gvi70000/Advanced-Weather-Station-V2/PGA460/PGA460.c

/***************************************************************************
 * @file [PGA460].h/.c
 * This file contains definitions, data structures, and functions
 * for interfacing with the PGA460 ultrasonic transducer driver.
 *
 * Copyright (c) [2024] Grozea Ion gvi70000
 * 
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
 * THE SOFTWARE IS PROVIDED "AS IS", WITHOUT WARRANTY OF ANY KIND, EXPRESS OR
 * IMPLIED, INCLUDING BUT NOT LIMITED TO THE WARRANTIES OF MERCHANTABILITY,
 * FITNESS FOR A PARTICULAR PURPOSE AND NONINFRINGEMENT. IN NO EVENT SHALL THE
 * AUTHORS OR COPYRIGHT HOLDERS BE LIABLE FOR ANY CLAIM, DAMAGES OR OTHER
 * LIABILITY, WHETHER IN AN ACTION OF CONTRACT, TORT OR OTHERWISE, ARISING FROM,
 * OUT OF OR IN CONNECTION WITH THE SOFTWARE OR THE USE OR OTHER DEALINGS IN
 * THE SOFTWARE.
 ***************************************************************************/

// TO BE USED WITH PGA460 Configuration Tool.html to generate registers values

#include <string.h>
#include <stdio.h>
#include <math.h>
#include "usart.h"
#include "tim.h"
#include "PGA460.h"
#include "debug.h"
#include "cordic.h"         /* CORDIC peripheral for atan2 and sqrt */

extern UART_HandleTypeDef huart3;
// Timeout for blocking UART transfers (ms). Increase for low baud rates.
#define PGA460_UART_TIMEOUT_MS  50U
// Array to hold the moment in time when the DECPL pin of each PGA460 goes high filled by TIM2 CH1/2/3 DM
extern volatile DecplTimes_t  ToF_Result[3];  
extern volatile uint8_t Decpl_RDY;


#ifndef M_PI
	#define M_PI 3.14159265358979323846f
#endif

// Conversion factor: half round-trip, microseconds ? seconds
#define TOF_US_TO_S					(1e-6f)   // = 1f * 1e-6
// Geometry 
// 3 transducers on a circle: cone base D = 100 mm, at 120deg.
// They form a cone with the reflector in the tip at 150mm from the base
// The cone semi angle is 17.745deg, the Tx-Reflector-Rx distance is 2x157.493=314.986mm
// if c=496um/us the burst will get to receiver after 635us
// if c=306um/us the burst will get to receiver after 1036us
// 6 pulses at 58kHz are 104us
// Time window of interst is from 600us to 1200us
	
#define PGA460_BASE_DIAMETER_UM				100000	// In micro meters
#define PGA460_DISTANCE_UM						316228	// In micro meters
#define PGA460_CAPTURE_DELAY_MS				70			// Delay for sensor measurement to complete

#define PGA_CMD_SIZE				3
#define PGA_READ_SIZE				4
#define PGA_WRITE_SIZE			5
#define PGA_CMD_COUNT				26
#define PGA_MAX_OBJECTS			8 // PGA460 supports up to 8 objects per measurement
#define PGA_OBJECTS_TRACKED	1	// Number of objects we want to track (Must be = PGA_MAX_OBJECTS)

#if PGA_OBJECTS_TRACKED > PGA_MAX_OBJECTS
	#error "PGA_OBJECTS_TRACKED cannot be greater than PGA_MAX_OBJECTS!"
#endif
#define PGA_OBJ_DATA_SIZE (2 + (PGA_OBJECTS_TRACKED * 4))

#define PGA460_TEMP_ERR	900.0f
#define ULTRASONIC_SENSOR_COUNT	3	// Number of ultrasonic sensors in the array

static const PGA460_Regs_t s0 = {
		.EEData.UserData = {0}, // 0x00..0x13
		.EEData.TVG = {
		.TVGAIN0 = 48, .TVGAIN1 = 80, .TVGAIN2 = 0, .TVGAIN3 = 255,
		.TVGAIN4 = 240, .TVGAIN5 = 0, .TVGAIN6 = 0
	},
	.EEData.Sett = {
		.INIT_GAIN		= 0,		// low initial gain (near target)
		.FREQUENCY		= 144,	// 58.0 kHz (0.2*140+30) CUSA center freq
		.DEADTIME			= 0,		// deglitch=32 us, pulse DT=0
		.PULSE_P1			= 102,	// IO_IF_SEL=0 (time-based), DIAG=1, P1=4 pulses
		.PULSE_P2			= 0,		// P2=0 pulses (addr=0)
		.CURR_LIM_P1	= 63,		// keep your hardware-safe limits
		.CURR_LIM_P2	= 0,
		.REC_LENGTH		= 0,		// 4.096 ms window per preset
		.FREQ_DIAG		= 16,		// standard diag enable
		.SAT_FDIAG_TH	= 0,		// TI typical
		.FVOLT_DEC		= 0,		// TI typical
		.DECPL_TEMP		= 0,		// TI typical
		.DSP_SCALE		= 0,
		.TEMP_TRIM		= 136,
		.P1_GAIN_CTRL = 0,
		.P2_GAIN_CTRL = 0
	},
		.eeCtrl = { .Val.Value = 0 },
//		.Filters = {
//		.BPF_A2_MSB=137, .BPF_A2_LSB=97, .BPF_A3_MSB=252, .BPF_A3_LSB=206, .BPF_B1_MSB=1,
//		.BPF_B1_LSB=153, .LPF_A2_MSB=128, .LPF_A2_LSB=205, .LPF_B1_MSB=0, .LPF_B1_LSB=103
//	},
//		.TestMux = { .Val.Value = 0 },
		.Stat0 = { .Val.Value = 0 },
		.Stat1 = { .Val.Value = 0 },
		.THR = {
		.P1_THR = {49, 65, 0, 0, 0, 0, 255, 255, 255, 255, 255, 255, 255, 255, 255, 7},
		.P2_THR = {49, 65, 0, 0, 0, 0, 248, 1, 255, 255, 255, 255, 255, 255, 255, 7}
		}
	};

static const PGA460_Regs_t s1 = {
		.EEData.UserData = {0}, // 0x00..0x13
		.EEData.TVG = {
		.TVGAIN0 = 48, .TVGAIN1 = 80, .TVGAIN2 = 0, .TVGAIN3 = 255,
		.TVGAIN4 = 240, .TVGAIN5 = 0, .TVGAIN6 = 0
	},
	.EEData.Sett = {
		.INIT_GAIN		= 0,		// low initial gain (near target)
		.FREQUENCY		= 144,	// 58.0 kHz (0.2*140+30) CUSA center freq
		.DEADTIME			= 0,		// deglitch=32 us, pulse DT=0
		.PULSE_P1			= 102,	// IO_IF_SEL=0 (time-based), DIAG=1, P1=4 pulses
		.PULSE_P2			= 32,		// P2=0 pulses (addr=0)
		.CURR_LIM_P1	= 63,		// keep your hardware-safe limits
		.CURR_LIM_P2	= 0,
		.REC_LENGTH		= 0,		// 4.096 ms window per preset
		.FREQ_DIAG		= 16,		// standard diag enable
		.SAT_FDIAG_TH	= 0,		// TI typical
		.FVOLT_DEC		= 0,		// TI typical
		.DECPL_TEMP		= 0,		// TI typical
		.DSP_SCALE		= 0,
		.TEMP_TRIM		= 136,
		.P1_GAIN_CTRL = 0,
		.P2_GAIN_CTRL = 0
	},
		.eeCtrl = { .Val.Value = 0 },
//		.Filters = {
//		.BPF_A2_MSB=137, .BPF_A2_LSB=97, .BPF_A3_MSB=252, .BPF_A3_LSB=206, .BPF_B1_MSB=1,
//		.BPF_B1_LSB=153, .LPF_A2_MSB=128, .LPF_A2_LSB=205, .LPF_B1_MSB=0, .LPF_B1_LSB=103
//	},
//		.TestMux = { .Val.Value = 0 },
		.Stat0 = { .Val.Value = 0 },
		.Stat1 = { .Val.Value = 0 },
		.THR = {
		.P1_THR = {49, 65, 0, 0, 0, 0, 255, 255, 255, 255, 255, 255, 255, 255, 255, 7},
		.P2_THR = {49, 65, 0, 0, 0, 0, 248, 1, 255, 255, 255, 255, 255, 255, 255, 7}
		}
	};

static const PGA460_Regs_t s2 = {
		.EEData.UserData = {0}, // 0x00..0x13
		.EEData.TVG = {
		.TVGAIN0 = 48, .TVGAIN1 = 80, .TVGAIN2 = 0, .TVGAIN3 = 255,
		.TVGAIN4 = 240, .TVGAIN5 = 0, .TVGAIN6 = 0
	},
	.EEData.Sett = {
		.INIT_GAIN		= 0,		// low initial gain (near target)
		.FREQUENCY		= 144,	// 58.0 kHz (0.2*140+30) CUSA center freq
		.DEADTIME			= 0,		// deglitch=32 us, pulse DT=0
		.PULSE_P1			= 102,	// IO_IF_SEL=0 (time-based), DIAG=1, P1=4 pulses
		.PULSE_P2			= 64,		// P2=0 pulses (addr=0)
		.CURR_LIM_P1	= 63,		// keep your hardware-safe limits
		.CURR_LIM_P2	= 0,
		.REC_LENGTH		= 0,		// 4.096 ms window per preset
		.FREQ_DIAG		= 16,		// standard diag enable
		.SAT_FDIAG_TH	= 0,		// TI typical
		.FVOLT_DEC		= 0,		// TI typical
		.DECPL_TEMP		= 0,		// TI typical
		.DSP_SCALE		= 0,
		.TEMP_TRIM		= 136,
		.P1_GAIN_CTRL = 0,
		.P2_GAIN_CTRL = 0
	},
		.eeCtrl = { .Val.Value = 0 },
//		.Filters = {
//		.BPF_A2_MSB=137, .BPF_A2_LSB=97, .BPF_A3_MSB=252, .BPF_A3_LSB=206, .BPF_B1_MSB=1,
//		.BPF_B1_LSB=153, .LPF_A2_MSB=128, .LPF_A2_LSB=205, .LPF_B1_MSB=0, .LPF_B1_LSB=103
//	},
//		.TestMux = { .Val.Value = 0 },
		.Stat0 = { .Val.Value = 0 },
		.Stat1 = { .Val.Value = 0 },
		.THR = {
		.P1_THR = {49, 65, 0, 0, 0, 0, 255, 255, 255, 255, 255, 255, 255, 255, 255, 7},
		.P2_THR = {49, 65, 0, 0, 0, 0, 248, 1, 255, 255, 255, 255, 255, 255, 255, 7}
		}
	};

// --- Array with 3 elements(sensors): [0] TVG, [1] Settings, [2] Thresholds ---
PGA460_Sensor_t sensors[ULTRASONIC_SENSOR_COUNT] = {{ .Registers = s0 }, { .Registers = s1 }, { .Registers = s2 }};

/**
 * @brief Read all EEPROM registers individually and log them via DEBUG().
 * @details Iterates addresses 0x00-0x2B, reads each with PGA460_RegisterRead(),
 *          and logs the named value.  Used during development to verify EEPROM
 *          contents after a bulk write or burn.
 *
 *          ONLY compiled when DEBUG_PGA460 is defined — each register read
 *          incurs a HAL_Delay(100), so the full scan takes ~4.4 s per sensor.
 *          Never call this in production firmware.
 * @param sensorID  Sensor UART address (0-7).
 */
#ifdef DEBUG_PGA460
static void PGA460_ReadAndPrintEEPROM(uint8_t sensorID) {
	DEBUG("Reading EEPROM registers for Sensor %u...\n", sensorID);
	uint8_t regValue = 0;
	for (uint8_t regAddr = 0x00; regAddr <= 0x2B; ++regAddr) {
		if (PGA460_RegisterRead(sensorID, regAddr, &regValue) == HAL_OK) {
			const char* regName;
			switch (regAddr) {
				case REG_USER_DATA1:  regName = "USER_DATA1";  break;
				case REG_USER_DATA2:  regName = "USER_DATA2";  break;
				case REG_USER_DATA3:  regName = "USER_DATA3";  break;
				case REG_USER_DATA4:  regName = "USER_DATA4";  break;
				case REG_USER_DATA5:  regName = "USER_DATA5";  break;
				case REG_USER_DATA6:  regName = "USER_DATA6";  break;
				case REG_USER_DATA7:  regName = "USER_DATA7";  break;
				case REG_USER_DATA8:  regName = "USER_DATA8";  break;
				case REG_USER_DATA9:  regName = "USER_DATA9";  break;
				case REG_USER_DATA10: regName = "USER_DATA10"; break;
				case REG_USER_DATA11: regName = "USER_DATA11"; break;
				case REG_USER_DATA12: regName = "USER_DATA12"; break;
				case REG_USER_DATA13: regName = "USER_DATA13"; break;
				case REG_USER_DATA14: regName = "USER_DATA14"; break;
				case REG_USER_DATA15: regName = "USER_DATA15"; break;
				case REG_USER_DATA16: regName = "USER_DATA16"; break;
				case REG_USER_DATA17: regName = "USER_DATA17"; break;
				case REG_USER_DATA18: regName = "USER_DATA18"; break;
				case REG_USER_DATA19: regName = "USER_DATA19"; break;
				case REG_USER_DATA20: regName = "USER_DATA20"; break;
				case REG_TVGAIN0:     regName = "TVGAIN0";     break;
				case REG_TVGAIN1:     regName = "TVGAIN1";     break;
				case REG_TVGAIN2:     regName = "TVGAIN2";     break;
				case REG_TVGAIN3:     regName = "TVGAIN3";     break;
				case REG_TVGAIN4:     regName = "TVGAIN4";     break;
				case REG_TVGAIN5:     regName = "TVGAIN5";     break;
				case REG_TVGAIN6:     regName = "TVGAIN6";     break;
				case REG_INIT_GAIN:   regName = "INIT_GAIN";   break;
				case REG_FREQUENCY:   regName = "FREQUENCY";   break;
				case REG_DEADTIME:    regName = "DEADTIME";    break;
				case REG_PULSE_P1:    regName = "PULSE_P1";    break;
				case REG_PULSE_P2:    regName = "PULSE_P2";    break;
				case REG_CURR_LIM_P1: regName = "CURR_LIM_P1"; break;
				case REG_CURR_LIM_P2: regName = "CURR_LIM_P2"; break;
				case REG_REC_LENGTH:  regName = "REC_LENGTH";  break;
				case REG_FREQ_DIAG:   regName = "FREQ_DIAG";   break;
				case REG_SAT_FDIAG_TH:regName = "SAT_FDIAG_TH";break;
				case REG_FVOLT_DEC:   regName = "FVOLT_DEC";   break;
				case REG_DECPL_TEMP:  regName = "DECPL_TEMP";  break;
				case REG_DSP_SCALE:   regName = "DSP_SCALE";   break;
				case REG_TEMP_TRIM:   regName = "TEMP_TRIM";   break;
				case REG_P1_GAIN_CTRL:regName = "P1_GAIN_CTRL";break;
				case REG_P2_GAIN_CTRL:regName = "P2_GAIN_CTRL";break;
				case REG_EE_CRC:      regName = "EE_CRC";      break;
				default:              regName = "UNKNOWN";      break;
			}
			DEBUG("  %s = 0x%02X\n", regName, regValue);
		} else {
			DEBUG("  0x%02X: read FAILED\n", regAddr);
		}
		HAL_Delay(100);
	}
	DEBUG("EEPROM read complete for sensor %u.\n", sensorID);
}
#endif /* DEBUG_PGA460 */

/**
 * @brief Compute the PGA460 UART frame checksum.
 * @details Sums all bytes in data[], folds any carry exceeding 0xFF by subtracting 255,
 *          and returns the bitwise complement of the 8-bit result.  The PGA460 protocol
 *          requires this checksum as the final byte of every outgoing frame.
 * @param data  Pointer to the byte array to checksum (typically CMD + payload).
 * @param len  Number of bytes to include in the sum.
 * @return Ones-complement checksum byte.
 */
static uint8_t PGA460_CalculateChecksum(const uint8_t *data, uint8_t len) {
	uint16_t carry = 0;
	for (uint8_t i = 0; i < len; i++) {
		carry += data[i];
		if (carry > 0xFF) {
			carry -= 255;
		}
	}
	return (uint8_t)(~carry & 0xFF);
}

/**
 * @brief Unlock or lock the PGA460 EEPROM by writing REG_EE_CTRL (0x40).
 * @details Sends a single-register write with PGA460_UNLOCK_EEPROM (0x68) to enable
 *          programming, or PGA460_LOCK_EEPROM (0x69) to trigger the burn and lock.
 *          Updates sensors[sensorID].Registers.eepromUnlocked on success.
 * @param sensorID  Sensor UART address (0-7).
 * @param unlock  1 = unlock (write 0x68); 0 = lock/burn (write 0x69).
 * @return HAL status.
 */
static HAL_StatusTypeDef PGA460_SetEEPROMAccess(const uint8_t sensorID, const uint8_t unlock) {
	uint8_t accessByte = unlock ? PGA460_UNLOCK_EEPROM : PGA460_LOCK_EEPROM;
	uint8_t cmd[5] = {PGA460_SYNC, (uint8_t)((sensorID << 5) | PGA460_CMD_REGISTER_WRITE), REG_EE_CTRL, accessByte, 0};
	cmd[4] = PGA460_CalculateChecksum(&cmd[1], 3); // Checksum over CMD, ADDR, DATA
	if (HAL_UART_Transmit(&huart3, cmd, sizeof(cmd), PGA460_UART_TIMEOUT_MS) != HAL_OK) {
		DEBUG("Sensor %d: EEPROM %s failed\n", sensorID, unlock ? "unlock" : "lock");
		return HAL_ERROR;
	}
	// Update status flag on success
	sensors[sensorID].Registers.eepromUnlocked = unlock ? 1 : 0;
	return HAL_OK;
}

/**
 * @brief PGA460_ScanAndReport function implementation.
 * @details Probes UART addresses 0-7 by reading REG_PULSE_P2 from each.  For each
 *          responding sensor, prints the UART address, the internal address stored in
 *          PULSE_P2[7:5], and the P2 pulse count.  Flags any address mismatch.
 *          Useful for initial bus setup and after PGA460_WriteUARTAddr().
 */
void PGA460_ScanAndReport(void) {
    uint8_t regValue = 0;
    uint8_t foundCount = 0;
    DEBUG("\n--- PGA460 Bus Scan (Addresses 0-7) ---\n");
    for (uint8_t addr = 0; addr <= 7; addr++) {
        if (PGA460_RegisterRead(addr, REG_PULSE_P2, &regValue) == HAL_OK) {
            foundCount++;
            uint8_t internalAddr = (regValue >> 5);
            uint8_t pulseCount   = (regValue & 0x1F);
            DEBUG("  [+] Sensor at UART addr %u  (stored addr=%u, P2 pulses=%u)\n",
                  addr, internalAddr, pulseCount);
            if (addr != internalAddr) {
                DEBUG("      [!] Address mismatch: listening on %u, register says %u\n",
                      addr, internalAddr);
            }
        }
        HAL_Delay(10);
    }
    if (foundCount == 0) {
        DEBUG("  [-] No sensors detected. Check power and wiring.\n");
    } else {
        DEBUG("--- Scan complete: %u sensor(s) found ---\n\n", foundCount);
    }
}

/**
 * @brief PGA460_WriteUARTAddr function implementation.
 * @details Scans the bus for the first responding sensor, writes the new UART address
 *          to REG_PULSE_P2[7:5] in RAM, then burns it to EEPROM so it persists.
 *          Steps: scan -> wake -> RAM write -> unlock -> burn -> verify.
 * @param targetAddr  New UART address to assign (0-7).
 * @return HAL status.
 */
HAL_StatusTypeDef PGA460_WriteUARTAddr(uint8_t targetAddr) {
uint8_t foundAddr = 0xFF;
    uint8_t regP2 = 0;
    uint8_t eeStatus = 0;
    // 1. SCAN: Find which address (0-7) responds
    for (uint8_t a = 0; a <= 7; a++) {
        if (PGA460_RegisterRead(a, REG_PULSE_P2, &regP2) == HAL_OK) {
            foundAddr = a;
            DEBUG("Found sensor at %u (Register says %u)\n", a, regP2);
            break;
        }
    }
    if (foundAddr == 0xFF) {
        DEBUG("No sensor found on bus.\n");
        return HAL_ERROR;
    }
    // 2. WAKE UP: Move digital core to READY state
    // Mandatory before EEPROM operations.
    PGA460_SetThresholds(foundAddr);
    HAL_Delay(50);
    // 3. RAM UPDATE: Set new address and ensure P2_PULSE = 0
    // Based on your requirement: targetAddr << 5
    uint8_t writeVal = (targetAddr << 5); 
    PGA460_RegisterWrite(foundAddr, REG_PULSE_P2, writeVal);
    HAL_Delay(50);
    // 4. BURN: Commit new address to EEPROM permanently.
    // PGA460_BurnEEPROM performs the full TI-specified two-step sequence
    // (write 0x68, wait 1 ms, write 0x69, wait 1000 ms, verify EE_PRGM_OK).
    // Do NOT write 0x68/0x69 manually here first — that would trigger two
    // consecutive burn cycles, wasting one of the 1000 guaranteed EEPROM cycles.
    DEBUG("Burning Address %u to EEPROM...\n", targetAddr);
    if (PGA460_BurnEEPROM(targetAddr) != HAL_OK) {
        DEBUG("Burn Command failed to send.\n");
        return HAL_ERROR;
    }
    // 5. WAIT & VERIFY
    HAL_Delay(100); // Wait for physical EEPROM write
    PGA460_RegisterRead(targetAddr, 0x40, &eeStatus);
    if (eeStatus & 0x80) {
        DEBUG("EEPROM ERROR: 0x%02X. Burn rejected.\n", eeStatus);
        return HAL_ERROR;
    }
    DEBUG("SUCCESS: Sensor set to Address %u\n", targetAddr);
    return HAL_OK;
}

EEImage_t *PGA460_GetEEData(uint8_t sensorID) {
    if (sensorID >= ULTRASONIC_SENSOR_COUNT) return NULL;
    return &sensors[sensorID].Registers.EEData;
}

/**
 * @brief PGA460_Init function implementation.
 * @details Initialises all three sensors in sequence.  For each sensor:
 *            1. Resets the Measures struct (tof_us, width, amplitude = 0).
 *            2. Writes the threshold map (mandatory to transition out of sleep).
 *          The burnEEPROM path is compiled but commented out; enable it when
 *          the final configuration needs committing to non-volatile storage.
 * @param burnEEPROM  1 = burn configuration to EEPROM flash after writing; 0 = RAM only.
 * @return HAL status.
 */
HAL_StatusTypeDef PGA460_Init(uint8_t burnEEPROM) {
	for (uint8_t i = 0; i < ULTRASONIC_SENSOR_COUNT; ++i) {
		// Step 1: Assign transducer config and reset measures
		sensors[i].Measures.tof_us		= 0;
		sensors[i].Measures.width			= 0;
		sensors[i].Measures.amplitude	= 0;
		// Step 2: Threshold write (uses current sensors[i].Registers.THR) !!! Mandatory step to start the sensor
		if (PGA460_SetThresholds(i) != HAL_OK) {
			DEBUG("Sensor %u: Threshold write failed!\n", i);
			return HAL_ERROR;
		}
		// Step 3: Read back full EEPROM image into sensors[i].Registers.EEData
		// This populates UserData[0..3] so Wind_LoadCalibration() can read path lengths
        if (PGA460_EEPROMBulkRead(i) != HAL_OK) {
            DEBUG("Sensor %u: EEPROM bulk read failed, UserData will be zero\n", i);
            // Non-fatal: Wind_LoadCalibration will fall back to NOMINAL_PATH_UM
        }
#ifdef DEBUG_PGA460
		/* Full register dump — ~4.4 s per sensor; only for bench verification. */
		PGA460_ReadAndPrintEEPROM(i);
#endif /* DEBUG_PGA460 */
//		// Step 2: EEPROM bulk write (shadow -> device)
//		if (PGA460_EEPROMBulkWrite(i) != HAL_OK) {
//			DEBUG("Sensor %u: EEPROM bulk write failed!\n", i);
//			return HAL_ERROR;
//		}
////		PGA460_ReadAndPrintEEPROM(i);
//		if(burnEEPROM) {
//			// Step 3: Optional EEPROM Burn
//			if (PGA460_BurnEEPROM(i) != HAL_OK) {
//				DEBUG("Sensor %u: EEPROM burn failed!\n", i);
//				return HAL_ERROR;
//			}
//		}
//		// Step 4: TVG write (push current TVG from mirror)
//		if (PGA460_SetTVG(i, PGA460_GAIN_58_90dB, &sensors[i].Registers.EEData.TVG) != HAL_OK) {
//				DEBUG("Sensor %u: TVG bulk write failed!\n", i);
//				return HAL_ERROR;
//		}
		// Step 5: Diagnostics/status
//		if (PGA460_CheckStatus(i) != HAL_OK) {
//			DEBUG("Sensor %u: Status check failed!\n", i);
//			//return HAL_ERROR;
//		}
//		// Frequency (Hz) via system diagnostics (diag=0)
//		float diagVal = 0.0f;
//		if (PGA460_GetSystemDiagnostics(i, 1, 0, &diagVal) == HAL_OK)
//				DEBUG("Sensor %u: Frequency Diagnostic = %.2f Hz\n", i, diagVal);
//		if (PGA460_GetSystemDiagnostics(i, 0, 1, &diagVal) == HAL_OK)
//				DEBUG("Sensor %u: Decay Period Diagnostic = %.2f us\n", i, diagVal);
//		if (PGA460_GetSystemDiagnostics(i, 0, 2, &diagVal) == HAL_OK)
//				DEBUG("Sensor %u: Die Temperature = %.2f C\n", i, diagVal);
//		if (PGA460_GetSystemDiagnostics(i, 0, 3, &diagVal) == HAL_OK)
//				DEBUG("Sensor %u: Noise Level = %.0f\n", i, diagVal);
//		// Step 7: Optional Echo Data Dump for verification
//		uint8_t echoBuf[128];
//		if (PGA460_GetEchoDataDump(i, PGA460_CMD_BURST_AND_LISTEN_PRESET1, echoBuf) != HAL_OK) {
//			DEBUG("Sensor %u: Echo Data Dump failed!\n", i);
//			return HAL_ERROR;
//		}
		
//		DEBUG("Sensor %u: Echo Data Dump:\n", i);
//		for (uint8_t j = 0; j < 128; ++j) {
//			DEBUG("%u%s", echoBuf[j], (j < 127) ? "," : "\n");
//		}
		DEBUG("-----\n");
		HAL_Delay(100);
	}
	return HAL_OK;
}

/**
 * @brief PGA460_RegisterRead function implementation.
 * @details Sends a 4-byte TX frame [SYNC][CMD][REG_ADDR][CHK] and reads the
 *          3-byte response [DIAG][DATA][CHK].  The DATA byte is returned in *regValue.
 *          The CMD byte encodes the sensor UART address in bits [7:5].
 * @param sensorID  Sensor UART address (0-7).
 * @param regAddr  Register address to read.
 * @param regValue  Output: register value.
 * @return HAL status.
 */
HAL_StatusTypeDef PGA460_RegisterRead(uint8_t sensorID, uint8_t regAddr, uint8_t *regValue) {
	// --- TX frame: [SYNC][CMD][REG_ADDR][CHK] ---
	uint8_t cmd[4] = {PGA460_SYNC, (uint8_t)((sensorID << 5) | PGA460_CMD_REGISTER_READ), regAddr, 0};
	cmd[3] = PGA460_CalculateChecksum(&cmd[1], 2); // Checksum over CMD + REG_ADDR
	if (HAL_UART_Transmit(&huart3, cmd, sizeof(cmd), PGA460_UART_TIMEOUT_MS) != HAL_OK) return HAL_ERROR;
	// --- RX frame: [DIAG][DATA][CHK] ---
	if (HAL_UART_Receive(&huart3, cmd, 3, PGA460_UART_TIMEOUT_MS) != HAL_OK) return HAL_ERROR;
	*regValue = cmd[1]; // DATA byte
	return HAL_OK;
}

/**
 * @brief PGA460_RegisterWrite function implementation.
 * @details Sends a 5-byte TX frame [SYNC][CMD][REG_ADDR][DATA][CHK].
 *          A 1 ms delay is applied after transmission; increase to 10 ms when writing
 *          TVG, threshold, or gain registers followed immediately by a read.
 * @param sensorID  Sensor UART address (0-7).
 * @param regAddr  Register address to write.
 * @param regValue  Value to write.
 * @return HAL status.
 */
HAL_StatusTypeDef PGA460_RegisterWrite(uint8_t sensorID, uint8_t regAddr, uint8_t regValue) {
	// TX frame: [SYNC][CMD][REG_ADDR][REG_VALUE][CHK]
	uint8_t cmd[5] = {PGA460_SYNC, (uint8_t)((sensorID << 5) | PGA460_CMD_REGISTER_WRITE), regAddr, regValue, 0};
	cmd[4] = PGA460_CalculateChecksum(&cmd[1], 3); // checksum over CMD+ADDR+DATA
	if (HAL_UART_Transmit(&huart3, cmd, sizeof(cmd), PGA460_UART_TIMEOUT_MS) != HAL_OK) return HAL_ERROR;
	// For commands 10 and 22: Wait 60 us if INIT_GAIN, TVG, THR or P1_GAIN_CTRL or P2_GAIN_CTRL
	// is written to before a read, otherwise wait 3.3 us for other functions.
	HAL_Delay(1); // Increase to 10 if needed
	return HAL_OK;
}

/**
 * @brief PGA460_CheckStatus function implementation.
 * @details Reads DEV_STAT0 (0x4C) and DEV_STAT1 (0x4D) and uses DEBUG() to report
 *          any active fault bits: EEPROM CRC errors, wakeup errors, thermal shutdown,
 *          and over/under-voltage conditions on VPWR, AVDD, and IOREG.
 * @param sensorID  Sensor UART address (0-7).
 * @return HAL status.
 */
HAL_StatusTypeDef PGA460_CheckStatus(uint8_t sensorID) {
	// Read both DEV_STAT registers
	if (PGA460_RegisterRead(sensorID, REG_DEV_STAT0, &sensors[sensorID].Registers.Stat0.Val.Value) != HAL_OK || PGA460_RegisterRead(sensorID, REG_DEV_STAT1, &sensors[sensorID].Registers.Stat1.Val.Value) != HAL_OK) {
		DEBUG("Sensor %d: Communication error! Could not read status registers.\n", (int)sensorID);
		return HAL_ERROR;
	}
	// --- DEV_STAT0 Flags ---
	if (sensors[sensorID].Registers.Stat0.Val.BitField.CMW_WU_ERR)
		DEBUG("Sensor %d: [CMW_WU_ERR] Wake-up error!\n", (int)sensorID);
	if (sensors[sensorID].Registers.Stat0.Val.BitField.THR_CRC_ERR)
		DEBUG("Sensor %d: [THR_CRC_ERR] Threshold CRC error!\n", (int)sensorID);
	if (sensors[sensorID].Registers.Stat0.Val.BitField.EE_CRC_ERR)
		DEBUG("Sensor %d: [EE_CRC_ERR] EEPROM CRC error!\n", (int)sensorID);
	if (sensors[sensorID].Registers.Stat0.Val.BitField.TRIM_CRC_ERR)
		DEBUG("Sensor %d: [TRIM_CRC_ERR] Trim CRC error!\n", (int)sensorID);
	// --- DEV_STAT1 Flags ---
	if (sensors[sensorID].Registers.Stat1.Val.BitField.TSD_PROT)
		DEBUG("Sensor %d: [TSD_PROT] Thermal shutdown occurred!\n", (int)sensorID);
	if (sensors[sensorID].Registers.Stat1.Val.BitField.IOREG_OV)
		DEBUG("Sensor %d: [IOREG_OV] IOREG Overvoltage!\n", (int)sensorID);
	if (sensors[sensorID].Registers.Stat1.Val.BitField.IOREG_UV)
		DEBUG("Sensor %d: [IOREG_UV] IOREG Undervoltage!\n", (int)sensorID);
	if (sensors[sensorID].Registers.Stat1.Val.BitField.AVDD_OV)
		DEBUG("Sensor %d: [AVDD_OV] AVDD Overvoltage!\n", (int)sensorID);
	if (sensors[sensorID].Registers.Stat1.Val.BitField.AVDD_UV)
		DEBUG("Sensor %d: [AVDD_UV] AVDD Undervoltage!\n", (int)sensorID);
	if (sensors[sensorID].Registers.Stat1.Val.BitField.VPWR_OV)
		DEBUG("Sensor %d: [VPWR_OV] VPWR Overvoltage!\n", (int)sensorID);
	if (sensors[sensorID].Registers.Stat1.Val.BitField.VPWR_UV)
		DEBUG("Sensor %d: [VPWR_UV] VPWR Undervoltage!\n", (int)sensorID);
	return HAL_OK;
}

/**
 * @brief PGA460_EEPROMBulkWrite function implementation.
 * @details Sends the 43-byte EEPROM payload (UserData[20] + TVG[7] + Settings[16])
 *          using CMD 0x0C.  EE_CRC (register 0x2B, the last byte of Settings_t) is
 *          intentionally excluded — the device auto-calculates and stores it on burn.
 *          Confirmed against TI USSC library calcChecksum (EEBW case): checksumLoops=44
 *          covers CMD + 43 data bytes; EE_CRC is never part of the bulk-write payload.
 *
 *          Frame layout: [SYNC][CMD][43 bytes][CHK]  = 45 bytes total.
 *          Checksum input: CMD + 43 data bytes = 44 bytes.
 * @param sensorID  Sensor UART address (0-7).
 * @return HAL status.
 */
HAL_StatusTypeDef PGA460_EEPROMBulkWrite(uint8_t sensorID) {
	// Step 1: Unlock EEPROM if needed
	if (sensors[sensorID].Registers.eepromUnlocked == 0) {
		if (PGA460_SetEEPROMAccess(sensorID, 1) != HAL_OK) {
			DEBUG("Sensor %d: EEPROM unlock failed before bulk write\n", sensorID);
			return HAL_ERROR;
		}
	}
	/* Step 2: Build 45-byte frame.
	 * EEImage_t = UserData[20] + TVG[7] + Settings[17] = 44 bytes.
	 * The last Settings byte is EE_CRC (auto-computed by the device; must NOT be
	 * sent).  We copy only 43 bytes (sizeof(EEImage_t) - 1).               */
	uint8_t frame[45] = {0};
	frame[0] = PGA460_SYNC;
	frame[1] = (uint8_t)((sensorID << 5) | PGA460_CMD_EEPROM_BULK_WRITE);
	memcpy(&frame[2], &sensors[sensorID].Registers.EEData, sizeof(EEImage_t) - 1u); /* 43 bytes, no EE_CRC */
	/* Checksum: CMD (frame[1]) + 43 data bytes = 44 inputs */
	frame[44] = PGA460_CalculateChecksum(&frame[1], 44u);
	// Step 3: Transmit
	if (HAL_UART_Transmit(&huart3, frame, sizeof(frame), PGA460_UART_TIMEOUT_MS) != HAL_OK) {
		DEBUG("Sensor %d: EEPROM Bulk Write Failed!\n", sensorID);
		return HAL_ERROR;
	}
	HAL_Delay(1);
	if (PGA460_SetEEPROMAccess(sensorID, 0) != HAL_OK) {
		DEBUG("Sensor %d: EEPROM lock failed after bulk write\n", sensorID);
		return HAL_ERROR;
	}
	return HAL_OK;
}

/**
 * @brief PGA460_EEPROMBulkRead function implementation.
 * @details Sends CMD 0x0B (EEPROM Bulk Read) and receives the 46-byte response:
 *          [DIAG][44 EEData bytes][CHK].  The 44 bytes are copied directly into
 *          sensors[sensorID].Registers.EEData, populating UserData[0..19], TVG,
 *          and Settings in one shot.  This must be called during PGA460_Init()
 *          so that Wind_LoadCalibration() can read path lengths from UserData[0..3].
 * @param sensorID  Sensor UART address (0-7).
 * @return HAL status.
 */
HAL_StatusTypeDef PGA460_EEPROMBulkRead(uint8_t sensorID) {
    // TX frame: [SYNC][CMD][CHK] ? 3 bytes
    uint8_t tx[3];
    tx[0] = PGA460_SYNC;
    tx[1] = (uint8_t)((sensorID << 5) | PGA460_CMD_EEPROM_BULK_READ);
    tx[2] = PGA460_CalculateChecksum(&tx[1], 1);

    if (HAL_UART_Transmit(&huart3, tx, sizeof(tx), PGA460_UART_TIMEOUT_MS) != HAL_OK) {
        DEBUG("Sensor %u: EEPROM Bulk Read TX failed\n", sensorID);
        return HAL_ERROR;
    }

    // RX frame: [DIAG][44 EEData bytes][CHK] ? 46 bytes
    uint8_t rx[46] = {0};
    if (HAL_UART_Receive(&huart3, rx, sizeof(rx), PGA460_UART_TIMEOUT_MS) != HAL_OK) {
        DEBUG("Sensor %u: EEPROM Bulk Read RX failed\n", sensorID);
        return HAL_ERROR;
    }

    // rx[0] = DIAG, rx[1..44] = EEData, rx[45] = CHK
    memcpy(&sensors[sensorID].Registers.EEData, &rx[1], sizeof(EEImage_t));

    DEBUG("Sensor %u: EEPROM Bulk Read OK - UserData[0..3] = %02X %02X %02X %02X\n",
          sensorID,
          sensors[sensorID].Registers.EEData.UserData[0],
          sensors[sensorID].Registers.EEData.UserData[1],
          sensors[sensorID].Registers.EEData.UserData[2],
          sensors[sensorID].Registers.EEData.UserData[3]);

    return HAL_OK;
}

/**
 * @brief PGA460_BurnEEPROM function implementation.
 * @details Executes the TI-specified two-step burn sequence on REG_EE_CTRL (0x40):
 *            1. Write 0x68 to begin the unlock sequence.
 *            2. Write 0x69 to start the internal charge pump and program the EEPROM.
 *            3. Wait 1000 ms (TI minimum; do not interrupt the sensor during this time).
 *            4. Read EE_CTRL back and verify bit 2 (EE_PRGM_OK) is set.
 *            5. Write 0x00 to leave EE_CTRL in a clean state.
 *          Use sparingly: the PGA460 EEPROM supports a limited number of burn cycles.
 * @param sensorID  Sensor UART address (0-7).
 * @return HAL status.
 */
HAL_StatusTypeDef PGA460_BurnEEPROM(uint8_t sensorID) {
    uint8_t burnStat = 0;
    // 1. Unlock EEPROM (0x68)
    if (PGA460_RegisterWrite(sensorID, 0x40, 0x68) != HAL_OK) {
        return HAL_ERROR;
    }
    HAL_Delay(1); // Short pause between unlock steps
    // 2. Trigger Burn (0x69)
    // Writing 0x69 sets the EEPRGM bit which initiates the internal charge pump
    if (PGA460_RegisterWrite(sensorID, 0x40, 0x69) != HAL_OK) {
        return HAL_ERROR;
    }
    // 3. WAIT (Crucial!) 
    // TI uses 1000ms. The process is slow. Do not interrupt the sensor here.
    HAL_Delay(1000);
    // 4. Read back status from EE_CNTRL
    if (PGA460_RegisterRead(sensorID, 0x40, &burnStat) != HAL_OK) {
        return HAL_ERROR;
    }
    // 5. Check Bit 2 (EE_PRGM_OK)
    if ((burnStat & 0x04) == 0x04) {
        DEBUG("Sensor %u: EEPROM Burn Successful (Status: 0x%02X)\n", sensorID, burnStat);
        // TI-style cleanup: Set back to 0 to lock
        PGA460_RegisterWrite(sensorID, 0x40, 0x00);
        return HAL_OK;
    } else {
        DEBUG("Sensor %u: Burn Failed (Status: 0x%02X, expected bit 2 set)\n", sensorID, burnStat);
        return HAL_ERROR;
    }
}

/**
 * @brief PGA460_GetTVG function implementation.
 * @details Sends CMD 0x0D (TVG Bulk Read) and receives [DIAG][TVGAIN0..TVGAIN6]
 *          (8 bytes total).  The 7 TVG bytes are copied into
 *          sensors[sensorID].Registers.EEData.TVG.  Returns HAL_ERROR if the
 *          response is all 0xFF (UART idle flood).
 * @param sensorID  Sensor UART address (0-7).
 * @return HAL status.
 */
HAL_StatusTypeDef PGA460_GetTVG(uint8_t sensorID) {
	// Send command [SYNC][CMD][CHK]
	uint8_t tx[3];
	tx[0] = PGA460_SYNC; // 0x55
	tx[1] = (uint8_t)((sensorID << 5) | (PGA460_CMD_TVG_BULK_READ)); // Command code
	tx[2] = PGA460_CalculateChecksum(&tx[1], 1);
	if (HAL_UART_Transmit(&huart3, tx, sizeof(tx), PGA460_UART_TIMEOUT_MS) != HAL_OK) {
		return HAL_ERROR;
	}
	// --- Step 2: Receive DIAG + 7 TVG bytes ---
	// RX: [DIAG][TVGAIN0..TVGAIN6] => 1 + 7 = 8 bytes
	uint8_t rx[8] = {0};
	if (HAL_UART_Receive(&huart3, rx, sizeof(rx), PGA460_UART_TIMEOUT_MS) != HAL_OK) {
		return HAL_ERROR;
	}
	// Optional: detect idle flood (all 0xFF)
	uint8_t idle = 1;
	for (uint32_t i = 0; i < sizeof(rx); i++) {
		if (rx[i] != 0xFF) {
			idle = 0;
			break;
		}
	}
	if (idle) return HAL_ERROR;
	// --- Step 3: Copy TVG bytes into mirror (skip rx[0] = DIAG) ---
	memcpy(&sensors[sensorID].Registers.EEData.TVG, &rx[1], sizeof(TVG_t));
	return HAL_OK;
}

/**
 * @brief PGA460_SetTVG function implementation.
 * @details Updates DECPL_TEMP[7:6] with the requested AFE gain range (preserving the
 *          lower 6 bits), then sends CMD 0x0E (TVG Bulk Write) with the 7-byte TVG
 *          payload.  Mirrors the written values into sensors[sensorID].Registers.
 * @param sensorID  Sensor UART address (0-7).
 * @param gain_range  AFE gain range (see PGA460_GainRange_t).
 * @param tvg  Pointer to the 7-byte TVG profile to write.
 * @return HAL status.
 */
HAL_StatusTypeDef PGA460_SetTVG(uint8_t sensorID, PGA460_GainRange_t gain_range, const TVG_t *tvg) {
	// 1) Update DECPL_TEMP[7:6] = AFE_GAIN_RNG, preserve other bits.
	sensors[sensorID].Registers.EEData.Sett.DECPL_TEMP = (sensors[sensorID].Registers.EEData.Sett.DECPL_TEMP & 0x3F) | gain_range;
	if (PGA460_RegisterWrite(sensorID, REG_DECPL_TEMP, sensors[sensorID].Registers.EEData.Sett.DECPL_TEMP) != HAL_OK) {
		return HAL_ERROR;
	}
	// 2) TVG bulk write: [SYNC][CMD=0x0E][7 TVG bytes][CHK]
	uint8_t frame[10];
	frame[0] = PGA460_SYNC;
	frame[1] = (uint8_t)((sensorID << 5) | (PGA460_CMD_TVG_BULK_WRITE));
	memcpy(&frame[2], tvg, sizeof(TVG_t)); // 7 bytes payload
	frame[9] = PGA460_CalculateChecksum(&frame[1], 1 + sizeof(TVG_t)); // checksum over CMD+DATA
	if (HAL_UART_Transmit(&huart3, frame, sizeof(frame), PGA460_UART_TIMEOUT_MS) != HAL_OK) {
		return HAL_ERROR;
	}
	// Mirror locally on success
	memcpy(&sensors[sensorID].Registers.EEData.TVG, tvg, sizeof(TVG_t));
	HAL_Delay(PGA460_CAPTURE_DELAY_MS);
	return HAL_OK;
}

/**
 * @brief PGA460_GetThresholds function implementation.
 * @details Sends CMD 0x0F (Threshold Bulk Read) and receives [DIAG][32 threshold bytes][CRC]
 *          (34 bytes total).  Copies the payload into sensors[sensorID].Registers.THR.
 * @param sensorID  Sensor UART address (0-7).
 * @return HAL status.
 */
HAL_StatusTypeDef PGA460_GetThresholds(uint8_t sensorID) {
	// 1) Send prebuilt command [SYNC][CMD][CHK]
	uint8_t tx[3];
	tx[0] = PGA460_SYNC; // 0x55
	tx[1] = (uint8_t)((sensorID << 5) | (PGA460_CMD_THRESHOLD_BULK_READ)); // Command code
	tx[2] = PGA460_CalculateChecksum(&tx[1], 1);
	if (HAL_UART_Transmit(&huart3, tx, sizeof(tx), PGA460_UART_TIMEOUT_MS) != HAL_OK) {
		return HAL_ERROR;
	}
	// 2) Receive DIAG (1) + THR block (33) = 34 bytes total
	uint8_t rx[34] = {0}; // rx[0]=DIAG, rx[1..32]=P1/P2 (32 bytes), rx[33]=THR_CRC
	if (HAL_UART_Receive(&huart3, rx, sizeof(rx), PGA460_UART_TIMEOUT_MS) != HAL_OK) {
		return HAL_ERROR;
	}
	// 3) Copy 33 bytes (P1_THR[16], P2_THR[16], THR_CRC) into mirror (skip DIAG)
	memcpy(&sensors[sensorID].Registers.THR, &rx[1], sizeof(Thresholds_t));
	return HAL_OK;
}

/**
 * @brief PGA460_SetThresholds function implementation.
 * @details Sends CMD 0x10 (Threshold Bulk Write) with the 33-byte threshold payload
 *          (P1_THR[16] + P2_THR[16] + THR_CRC) from sensors[sensorID].Registers.THR.
 *          This is a mandatory initialisation step to transition the sensor out of sleep.
 * @param sensorID  Sensor UART address (0-7).
 * @return HAL status.
 */
HAL_StatusTypeDef PGA460_SetThresholds(uint8_t sensorID) {
	// Build a 33-byte image (P1[16] + P2[16] + CRC) without mutating shadow yet
	uint8_t frame[35] = {0};
	frame[0] = PGA460_SYNC;
	frame[1] = (uint8_t)((sensorID << 5) | (PGA460_CMD_THRESHOLD_BULK_WRITE));
	memcpy(&frame[2], &sensors[sensorID].Registers.THR, 32);
	// Frame: [SYNC][CMD=0x10][33 bytes][CHK] => total 36 bytes
	frame[34] = PGA460_CalculateChecksum(&frame[1], 33); // checksum over CMD + 33 data bytes
	if (HAL_UART_Transmit(&huart3, frame, sizeof(frame), PGA460_UART_TIMEOUT_MS) != HAL_OK) {
		return HAL_ERROR;
	}
	HAL_Delay(PGA460_CAPTURE_DELAY_MS);
	return HAL_OK;
}

/**
 * @brief PGA460_UltrasonicCmd function implementation.
 * @details Builds and transmits the appropriate UART frame for the requested command:
 *            4-byte frame for burst/listen, temp/noise, and result-read commands.
 *            3-byte frame for echo dump and broadcast commands.
 *          For broadcast commands (address >= 0x11) the address field in CMD is 0.
 *          For burst/listen commands with noWait = 0, waits PGA460_CAPTURE_DELAY_MS
 *          (70 ms) after transmission to allow the measurement window to complete.
 * @param sensorID  Sensor UART address (0-7).
 * @param cmd  Command code (see PGA460_Command_t).
 * @param noWait  1 = return immediately; 0 = delay after burst commands.
 * @return HAL status.
 */
HAL_StatusTypeDef PGA460_UltrasonicCmd(const uint8_t sensorID, const PGA460_Command_t cmd, const uint8_t noWait) {
    uint8_t frame[4];
    uint16_t len = 0;
    frame[0] = PGA460_SYNC; // 0x55
    // Check if the command is a broadcast command (0x11 to 0x19).
    // If so, force the address bits to 0. Otherwise, use the sensorID.
    uint8_t addr = (cmd >= PGA460_CMD_BROADCAST_BURST_AND_LISTEN_P1) ? 0 : sensorID;
    // Pack the address into the top 3 bits and the command into the bottom 5 bits.
    frame[1] = (uint8_t)((addr << 5) | (cmd)); 
    switch (cmd) {
        // 4-byte frames: [SYNC][CMD][OBJ][CHK]
        case PGA460_CMD_BURST_AND_LISTEN_PRESET1:
        case PGA460_CMD_BURST_AND_LISTEN_PRESET2:
        case PGA460_CMD_LISTEN_ONLY_PRESET1:
        case PGA460_CMD_LISTEN_ONLY_PRESET2:
        case PGA460_CMD_BROADCAST_BURST_AND_LISTEN_P1:
        case PGA460_CMD_BROADCAST_BURST_AND_LISTEN_P2:
        case PGA460_CMD_BROADCAST_LISTEN_ONLY_P1:
        case PGA460_CMD_BROADCAST_LISTEN_ONLY_P2:
            frame[2] = PGA_OBJECTS_TRACKED; // 0x01
            frame[3] = PGA460_CalculateChecksum(&frame[1], 2); // Covers CMD + OBJ
            len = 4;
            break;
        // 3-byte frames: [SYNC][CMD][CHK]
        case PGA460_CMD_TEMP_AND_NOISE_MEASUREMENT:
        case PGA460_CMD_ULTRASONIC_MEASUREMENT_RESULT:
        case PGA460_CMD_TEMP_AND_NOISE_RESULT:
        case PGA460_CMD_TRANSDUCER_ECHO_DATA_DUMP:
        case PGA460_CMD_SYSTEM_DIAGNOSTICS:
        case PGA460_CMD_BROADCAST_TEMP_NOISE_MEASURE:
            frame[2] = PGA460_CalculateChecksum(&frame[1], 1); // Covers only CMD
            len = 3;
            break;
        default:
            DEBUG("Sensor %d: Unsupported CMD 0x%02X\n", sensorID, (unsigned)cmd);
            return HAL_ERROR;
    }
    if (HAL_UART_Transmit(&huart3, frame, len, PGA460_UART_TIMEOUT_MS) != HAL_OK) {
        DEBUG("Sensor %d: Ultrasonic TX failed (CMD=0x%02X)\n", sensorID, frame[1]);
        return HAL_ERROR;
    }
    // Only burst/listen & listen-only start a capture; give them time to run.
    if (!noWait && (len == 4)) {
        HAL_Delay(PGA460_CAPTURE_DELAY_MS); // ~70 ms
    }
		return HAL_OK;
}

/**
 * @brief PGA460_GetUltrasonicMeasurement function implementation.
 * @details Sends CMD 0x05 (Ultrasonic Measurement Result) and receives the response.
 *          Iterates through up to PGA_OBJECTS_TRACKED objects; stores the first valid
 *          result (rawTOF > 0 and != 0xFFFF) into sensors[sensorID].Measures.
 * @param sensorID  Sensor UART address (0-7).
 * @return HAL status.
 */
HAL_StatusTypeDef PGA460_GetUltrasonicMeasurement(const uint8_t sensorID) {
	uint8_t localBuffer[PGA_OBJ_DATA_SIZE] = {0};
	uint8_t tx[3];
	tx[0] = PGA460_SYNC; // 0x55
	tx[1] = (uint8_t)((sensorID << 5) | (PGA460_CMD_ULTRASONIC_MEASUREMENT_RESULT)); // Command code
	tx[2] = PGA460_CalculateChecksum(&tx[1], 1);
    // 1) Request UMR
    if (HAL_UART_Transmit(&huart3, tx, sizeof(tx), PGA460_UART_TIMEOUT_MS) != HAL_OK) {
        DEBUG("Sensor %d: Measurement Result Request Failed!\n", sensorID);
        return HAL_ERROR;
    }
    // 2) Read response
    if (HAL_UART_Receive(&huart3, localBuffer, sizeof(localBuffer), PGA460_UART_TIMEOUT_MS) != HAL_OK) {
        DEBUG("Sensor %d: Measurement Result Retrieval Failed!\n", sensorID);
        return HAL_ERROR;
    }
    HAL_StatusTypeDef status = HAL_ERROR;
    uint8_t stored = 0;
    // 3) Parse each object, store first valid into sensors[sensorID].Measures
    for (uint8_t i = 0; i < PGA_OBJECTS_TRACKED; i++) {
        const uint8_t base = 2 + (i * 4); // skip 2-byte diagnostic header
        const uint16_t rawTOF   = ((uint16_t)localBuffer[base] << 8) | localBuffer[base + 1];
        const uint8_t  widthRaw = localBuffer[base + 2];
        const uint8_t  amplitude = localBuffer[base + 3];
        //DEBUG("Sensor %d: Raw TOF = %04X\n", sensorID, rawTOF);
        if (rawTOF > 0 && rawTOF != 0xFFFF) {
            const uint16_t width_us = (uint16_t)widthRaw * 16;
            if (!stored) {
                sensors[sensorID].Measures.tof_us    = rawTOF;
                sensors[sensorID].Measures.width     = (uint8_t)((width_us > 255) ? 255 : width_us);
                sensors[sensorID].Measures.amplitude = amplitude;
                stored = 1;
            }
            status = HAL_OK;
        } else {
            DEBUG("Sensor %d: Obj %u -> Invalid (TOF = 0x%04X)\n", sensorID, (unsigned)(i + 1), rawTOF);
        }
    }
    return status;
}

/**
 * @brief PGA460_GetEchoDataDump function implementation.
 * @details Enables Echo Data Dump mode in REG_EE_CTRL (bit 7), triggers the requested
 *          preset, sends CMD 0x07, and receives 130 bytes (2-byte header + 128 bins).
 *          Disables the mode on exit.  Uses goto cleanup to ensure the mode is always
 *          disabled even on error.
 * @param sensorID  Sensor UART address (0-7).
 * @param preset  Preset command to trigger (CMD_BURST_AND_LISTEN_PRESET1 or PRESET2).
 * @param echoOut  Output buffer for 128 amplitude bytes (caller must provide 128 bytes).
 * @return HAL status.
 */
HAL_StatusTypeDef PGA460_GetEchoDataDump(uint8_t sensorID, uint8_t preset, uint8_t *echoOut) {
	HAL_StatusTypeDef ret = HAL_OK;
	uint8_t response[ECHO_DATA_TOTAL_BYTES] = {0}; // 2-byte header + 128 bins
	// 1) Enable Echo Data Dump Mode (EE_CTRL.DATADUMP_EN = 1)
	if (PGA460_RegisterWrite(sensorID, REG_EE_CTRL, ECHO_DATA_DUMP_ENABLE) != HAL_OK) {
		DEBUG("Sensor %d: Failed to enable Echo Data Dump mode!\n", sensorID);
		return HAL_ERROR;
	}
	HAL_Delay(10);
	// 2) Trigger the requested preset (burst+listen or listen-only)
	if (PGA460_UltrasonicCmd(sensorID, (PGA460_Command_t)preset, 0) != HAL_OK) {
		DEBUG("Sensor %d: Echo trigger preset failed!\n", sensorID);
		ret = HAL_ERROR;
		goto cleanup_disable_dump;
	}
	HAL_Delay(PGA460_CAPTURE_DELAY_MS); // allow full capture (~65 ms)
	// 3) Request Bulk Echo Data Dump (CMD = 0x07)
	uint8_t tx[3];
	tx[0] = PGA460_SYNC; // 0x55
	tx[1] = (uint8_t)((sensorID << 5) | (PGA460_CMD_TRANSDUCER_ECHO_DATA_DUMP)); // Command code
	tx[2] = PGA460_CalculateChecksum(&tx[1], 1);
	if (HAL_UART_Transmit(&huart3, tx, sizeof(tx), PGA460_UART_TIMEOUT_MS) != HAL_OK) {
		DEBUG("Sensor %d: Echo Data Dump request TX failed!\n", sensorID);
		ret = HAL_ERROR;
		goto cleanup_disable_dump;
	}
	// 4) Receive Echo Data Dump (2-byte header + 128 samples)
	if (HAL_UART_Receive(&huart3, response, sizeof(response), PGA460_UART_TIMEOUT_MS) != HAL_OK) {
		DEBUG("Sensor %d: Echo Data Dump RX failed!\n", sensorID);
		ret = HAL_ERROR;
		goto cleanup_disable_dump;
	}
	// 5) Copy only the 128 echo bins (skip the 2-byte header)
	memcpy(echoOut, &response[2], 128);
cleanup_disable_dump:
	// 6) Disable Echo Data Dump Mode (best-effort)
	// The previous status should be preserved. The return value should not be overwritten.
	if (PGA460_RegisterWrite(sensorID, REG_EE_CTRL, ECHO_DATA_DUMP_DISABLE) != HAL_OK) {
		DEBUG("Sensor %d: Failed to disable Echo Data Dump mode!\n", sensorID);
	}
	// Return the status from the main operation, not the cleanup operation.
	return ret;
}

/**
 * @brief PGA460_SetTemperatureOffset function implementation.
 * @details Reads the PGA460 internal temperature, computes (externalTempC - internal),
 *          clamps the signed offset to [-64, +63] degrees, encodes it as sign-magnitude
 *          in REG_TEMP_TRIM (bit 7 = sign, bits 6:0 = magnitude), and writes it to the
 *          device.  Mirrors the new value into sensors[sensorID].Registers.
 * @param sensorID  Sensor UART address (0-7).
 * @param externalTempC  Reference temperature in degrees Celsius (from BMP581 or HDC302x).
 * @return HAL status.
 */
HAL_StatusTypeDef PGA460_SetTemperatureOffset(uint8_t sensorID, float externalTempC) {
	// 1) Read internal temperature
	float internalTempC = PGA460_ReadTemperatureOrNoise(sensorID, PGA460_CMD_GET_TEMP);
	if (internalTempC == PGA460_TEMP_ERR) {
		DEBUG("Sensor %d: Failed to read internal temperature!\n", sensorID);
		return HAL_ERROR;
	}
	DEBUG("Sensor %d: Internal Temperature = %.2f C\n", sensorID, internalTempC);
	// 2) Compute signed offset (external - internal), clamp to [-64, +63]
	int8_t offset = (int8_t)roundf(externalTempC - internalTempC);
	if (offset >  63)
		offset =  63;
	if (offset < -64)
		offset = -64;
	// 3) Read current TEMP_TRIM (0x28)
	uint8_t tempTrim = 0;
	if (PGA460_RegisterRead(sensorID, REG_TEMP_TRIM, &tempTrim) != HAL_OK) {
		DEBUG("Sensor %d: Failed to read TEMP_TRIM register!\n", sensorID);
		return HAL_ERROR;
	}
	DEBUG("Sensor %d: Original TEMP_TRIM = 0x%02X\n", sensorID, tempTrim);
	// 4) Build sign-magnitude byte: bit7 = sign, bits6:0 = magnitude
	uint8_t magnitude = (uint8_t)((offset < 0) ? -offset : offset);
	uint8_t signedOffset = ((offset < 0) ? 0x80 : 0x00) | (magnitude & 0x7F);
	// If TEMP_TRIM has no reserved bits, write the whole byte:
	tempTrim = signedOffset;
	// 5) Write updated TEMP_TRIM
	if (PGA460_RegisterWrite(sensorID, REG_TEMP_TRIM, tempTrim) != HAL_OK) {
		DEBUG("Sensor %d: Failed to write TEMP_TRIM register!\n", sensorID);
		return HAL_ERROR;
	}
	// Mirror locally on success
	sensors[sensorID].Registers.EEData.Sett.TEMP_TRIM = tempTrim;
	DEBUG("Sensor %d: New TEMP_TRIM = 0x%02X (Offset: %+d C)\n", sensorID, tempTrim, offset);
	return HAL_OK;
}

/**
 * @brief PGA460_GetSystemDiagnostics function implementation.
 * @details Optionally triggers a Preset 1 burst (run = 1), then sends CMD 0x08
 *          (System Diagnostics) and receives the 4-byte response.
 *          The diag parameter selects the returned value:
 *            0 = transducer frequency in Hz (from FREQ_TICKS at 0.5 us per tick)
 *            1 = echo decay period in us (DECAY_TICKS * 16)
 *            2 = internal die temperature in deg C (via PGA460_ReadTemperatureOrNoise)
 *            3 = ambient noise level, raw 8-bit (via PGA460_ReadTemperatureOrNoise)
 * @param sensorID  Sensor UART address (0-7).
 * @param run  1 = trigger a burst before reading; 0 = use the last stored result.
 * @param diag  0 = frequency, 1 = decay period, 2 = temperature, 3 = noise.
 * @param diagResult  Output: diagnostic value in units described above.
 * @return HAL status.
 */
HAL_StatusTypeDef PGA460_GetSystemDiagnostics(const uint8_t sensorID, const uint8_t run, const uint8_t diag, float *diagResult) {
	// Optional: start a capture using P1 before running diagnostics
	if (run) {
		if (PGA460_UltrasonicCmd(sensorID, PGA460_CMD_BURST_AND_LISTEN_PRESET1, 0) != HAL_OK) {
			DEBUG("Sensor %d: Burst-and-Listen Command Failed!\n", sensorID);
			return HAL_ERROR;
		}
		HAL_Delay(5); // allow measurement to complete
	}
	// Send System Diagnostics (0x08) ? 3B command [SYNC][CMD][CHK]
	uint8_t cmd[4] = {PGA460_SYNC, (uint8_t)((sensorID << 5) | PGA460_CMD_SYSTEM_DIAGNOSTICS), 0, 0};
	cmd[2] = PGA460_CalculateChecksum(&cmd[1], 1);
	if (HAL_UART_Transmit(&huart3, cmd, 3, PGA460_UART_TIMEOUT_MS) != HAL_OK) {
		DEBUG("Sensor %d: System Diagnostics Request Failed!\n", sensorID);
		return HAL_ERROR;
	}
	// Receive 4B response: [DIAG][FREQ_TICKS][DECAY_TICKS][PCHK]
	if (HAL_UART_Receive(&huart3, cmd, sizeof(cmd), PGA460_UART_TIMEOUT_MS) != HAL_OK) {
		DEBUG("Sensor %d: System Diagnostics Retrieval Failed!\n", sensorID);
		return HAL_ERROR;
	}
	// Special cases handled via temp/noise helper
	if (diag == 2) {  // Temperature (degC)
		*diagResult = PGA460_ReadTemperatureOrNoise(sensorID, PGA460_CMD_GET_TEMP);
		if (*diagResult == PGA460_TEMP_ERR) {
			DEBUG("Sensor %d: Failed to Retrieve Temperature!\n", sensorID);
			return HAL_ERROR;
		}
		return HAL_OK;
	}
	if (diag == 3) {  // Noise (raw 8-bit)
		*diagResult = PGA460_ReadTemperatureOrNoise(sensorID, PGA460_CMD_GET_NOISE);
		if (*diagResult == PGA460_TEMP_ERR) {
			DEBUG("Sensor %d: Failed to Retrieve Noise!\n", sensorID);
			return HAL_ERROR;
		}
		return HAL_OK;
	}
	// Standard diagnostics
	switch (diag) {
		case 0: { // Frequency (Hz) from ticks of 0.5 us
			const uint8_t ticks = cmd[1];
			if (ticks == 0) {
				DEBUG("Sensor %d: Invalid Frequency Value (0 ticks)!\n", sensorID);
				return HAL_ERROR;
			}
			*diagResult = 1.0f / (ticks * 0.5e-6f); // Hz
			break;
		}
		case 1: { // Decay period (us), tick = 16 us
			*diagResult = (float)cmd[2] * 16.0f; // us
			break;
		}
		default:
			DEBUG("Sensor %d: Invalid Diagnostic Type (%u)!\n", sensorID, (unsigned)diag);
			return HAL_ERROR;
	}
	//DEBUG("Sensor %d: Diagnostic [%u] Result: %.2f\n", sensorID, (unsigned)diag, *diagResult);
	return HAL_OK;
}

/**
 * @brief PGA460_ReadTemperatureOrNoise function implementation.
 * @details Sends CMD 0x04 (Temp/Noise Measurement) with the mode selector byte,
 *          waits PGA460_CAPTURE_DELAY_MS, then sends CMD 0x06 (Temp/Noise Result)
 *          and receives the 4-byte response [DIAG][TEMP][NOISE][CHK].
 *          Temperature: T_C = (raw_byte - 64) / 1.5
 *          Noise: returned as the raw 8-bit amplitude byte.
 * @param sensorID  Sensor UART address (0-7).
 * @param mode  PGA460_CMD_GET_TEMP or PGA460_CMD_GET_NOISE.
 * @return Temperature in deg C, noise as raw byte, or PGA460_TEMP_ERR (999.0f) on failure.
 */
float PGA460_ReadTemperatureOrNoise(const uint8_t sensorID, const PGA460_CmdType_t mode) {
	const uint8_t isNoise = (mode == PGA460_CMD_GET_NOISE);
	float result = PGA460_TEMP_ERR;  // default invalid
	// Step 1: Request Temperature or Noise Measurement
	// [SYNC][CMD=0x04][SEL(0=temp,1=noise)][CHK(CMD+SEL)]
	uint8_t cmd[4] = {PGA460_SYNC, (uint8_t)((sensorID << 5) | PGA460_CMD_TEMP_AND_NOISE_MEASUREMENT), isNoise ? 1 : 0, 0};
	cmd[3] = PGA460_CalculateChecksum(&cmd[1], 2); // over CMD+SEL
	if (HAL_UART_Transmit(&huart3, cmd, sizeof(cmd), PGA460_UART_TIMEOUT_MS) != HAL_OK) {
		DEBUG("Sensor %d: Temp/Noise Measurement Command Failed!\n", sensorID);
		return result;
	}
	HAL_Delay(PGA460_CAPTURE_DELAY_MS);  // small settle for measurement to complete
	// Step 2: Send command to read the result (fixed 3-byte command)
	cmd[1] = (uint8_t)((sensorID << 5) | (PGA460_CMD_TEMP_AND_NOISE_RESULT)); // CMD
	cmd[2] = PGA460_CalculateChecksum(&cmd[1], 1); // over CMD+SEL
	if (HAL_UART_Transmit(&huart3, cmd, PGA_CMD_SIZE, PGA460_UART_TIMEOUT_MS) != HAL_OK) {
		DEBUG("Sensor %d: Result Request Command Failed!\n", sensorID);
		return result;
	}
	// Step 3: Read 4-byte result frame: [DIAG][TEMP][NOISE][PCHK]
	if (HAL_UART_Receive(&huart3, cmd, sizeof(cmd), PGA460_UART_TIMEOUT_MS) != HAL_OK) {
		DEBUG("Sensor %d: Failed to Receive Temp/Noise Data!\n", sensorID);
		return result;
	}
	// Step 4: Parse result
	if (!isNoise) {
		result = ((float)cmd[1] - 64.0f) / 1.5f;  // Temperature in degC
		//DEBUG("Sensor %d: Temperature (C) = %.2f\n", sensorID, result);
	} else {
		result = (float)cmd[2]; // Noise level (raw 8-bit)
		//DEBUG("Sensor %d: Noise Level = %.2f\n", sensorID, result);
	}
	return result;
}
