gvi70000/Advanced-Weather-Station-V2/TSL25911/TSL25911.c

/***************************************************************************
 * @file [TSL25911].h/.c
 * This file contains definitions, data structures, and functions
 * for interfacing with the TSL25911 very-high sensitivity light-to-digital converter.
 *
 * Copyright (c) [2024] Grozea Ion gvi70000
 * 
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
 * THE SOFTWARE IS PROVIDED "AS IS", WITHOUT WARRANTY OF ANY KIND, EXPRESS OR
 * IMPLIED, INCLUDING BUT NOT LIMITED TO THE WARRANTIES OF MERCHANTABILITY,
 * FITNESS FOR A PARTICULAR PURPOSE AND NONINFRINGEMENT. IN NO EVENT SHALL THE
 * AUTHORS OR COPYRIGHT HOLDERS BE LIABLE FOR ANY CLAIM, DAMAGES OR OTHER
 * LIABILITY, WHETHER IN AN ACTION OF CONTRACT, TORT OR OTHERWISE, ARISING FROM,
 * OUT OF OR IN CONNECTION WITH THE SOFTWARE OR THE USE OR OTHER DEALINGS IN
 * THE SOFTWARE.
 ***************************************************************************/

#include "TSL25911.h"
#include "i2c.h"

/** 
 * @brief External declaration for the I2C handle.
 * The handle is used for I2C communication with the TSL2591 sensor.
 */
extern I2C_HandleTypeDef hi2c1;

/**
 * @brief Static instance of TSL2591 register structure.
 * This structure holds the configuration and status data for the sensor.
 */
static TSL25911_REGISTERS_t TSL25911_Sensor;

// Write to a register of TSL2591
static inline HAL_StatusTypeDef TSL25911_WriteRegister(uint8_t reg, uint8_t* data, uint8_t len) {
    return WriteRegister(TSL25911_I2C_ADDR, reg, data, len, &hi2c1);
}

// Read from a register of TSL2591
static inline HAL_StatusTypeDef TSL25911_ReadRegister(uint8_t reg, uint8_t* data, uint8_t len) {
    return ReadRegister(TSL25911_I2C_ADDR, reg, data, len, &hi2c1);
}

/**
 * @brief Initializes the TSL25911 sensor.
 * 
 * This function follows the initialization sequence:
 * 1. Reads and validates the chip ID.
 * 2. Powers on the oscillator by setting the PON bit.
 * 3. Configures gain and integration time.
 * 4. Configures ALS interrupt thresholds.
 * 5. Enables ALS and ALS interrupts.
 * 
 * @return HAL_OK if successful, HAL_ERROR otherwise.
 */
HAL_StatusTypeDef TSL25911_Init(void) {
    // Step 1: Get and validate chip ID
    if (TSL25911_ReadID() != HAL_OK || TSL25911_Sensor.ID != TSL25911_ID) {
        return HAL_ERROR;
    }

    // Step 2: Power ON the oscillator by setting the PON bit
    if (TSL25911_Enable(TSL25911_STATE_PON) != HAL_OK) {
        return HAL_ERROR;
    }
    HAL_Delay(10);  // Wait for oscillator stabilization

    // Step 3: Configure gain and integration time
    // 500 ms x 2 persist cycles = 1000 ms interrupt period
    if (TSL25911_SetGainAndIntegrationTime(TSL25911_GAIN_LOW, TSL25911_INTEGRATION_600MS) != HAL_OK) {
        return HAL_ERROR;
    }

    // Step 4: Configure ALS interrupt thresholds
    // Both set to 0xFFFF so every reading is always out of range,
    // guaranteeing an interrupt fires every persist cycle
    if (TSL25911_SetInterruptThresholds(0xFFFF, 0xFFFF) != HAL_OK) {
        return HAL_ERROR;
    }

    // Step 5: Set persistence to 2 cycles: 2 x 500 ms = ~1000 ms interrupt rate
    if (TSL25911_SetPersistence(TSL25911_PERSIST_2_CYCLES) != HAL_OK) {
        return HAL_ERROR;
    }

    // Step 6: Enable ALS and ALS interrupts
    if (TSL25911_Enable(TSL25911_STATE_PON_AEN_AIEN) != HAL_OK) {
        return HAL_ERROR;
    }

    return HAL_OK;
}

/**
 * @brief Enables or disables the TSL2591 sensor.
 * 
 * @param state Desired state for the sensor (e.g., TSL25911_STATE_DISABLED or TSL25911_STATE_ENABLE).
 * @return HAL_OK if successful, HAL_ERROR otherwise.
 */
HAL_StatusTypeDef TSL25911_Enable(TSL25911_STATE_t state) {
    TSL25911_Sensor.ENABLE.Val.Value = state;
    return TSL25911_WriteRegister(TSL25911_REG_ENABLE, &TSL25911_Sensor.ENABLE.Val.Value, 1);
}

/**
 * @brief Resets the TSL2591 sensor.
 * 
 * This function sets the SRESET bit in the CONTROL register to reset the sensor.
 * @return HAL_OK if successful, HAL_ERROR otherwise.
 */
HAL_StatusTypeDef TSL25911_Reset(void) {
    TSL25911_Sensor.CTRL.Val.BitField.SRESET = 1;
    return TSL25911_WriteRegister(TSL25911_REG_CONTROL, &TSL25911_Sensor.CTRL.Val.Value, 1);
}

/**
 * @brief Sets the gain and integration time for the TSL2591 sensor.
 * 
 * @param gain Desired gain setting.
 * @param integrationTime Desired integration time setting.
 * @return HAL_OK if successful, HAL_ERROR otherwise.
 */
HAL_StatusTypeDef TSL25911_SetGainAndIntegrationTime(TSL25911_GAIN_t gain, TSL25911_INTEGRATION_t integrationTime) {
    TSL25911_Sensor.CTRL.Val.BitField.AGAIN = gain;
    TSL25911_Sensor.CTRL.Val.BitField.ATIME = integrationTime;
    return TSL25911_WriteRegister(TSL25911_REG_CONTROL, &TSL25911_Sensor.CTRL.Val.Value, 1);
}

/**
 * @brief Configures the ALS interrupt thresholds.
 * 
 * @param low Low threshold value.
 * @param high High threshold value.
 * @return HAL_OK if successful, HAL_ERROR otherwise.
 */
HAL_StatusTypeDef TSL25911_SetInterruptThresholds(uint16_t low, uint16_t high) {
    TSL25911_Sensor.ALS.LowThreshold.Value = low;
    TSL25911_Sensor.ALS.HighThreshold.Value = high;

    // Write thresholds to the sensor
    HAL_StatusTypeDef status = TSL25911_WriteRegister(TSL25911_REG_AILTL, TSL25911_Sensor.ALS.FullArray, 4);
    if (status != HAL_OK) return status;

    // Set No Persist Interrupt Thresholds
    return TSL25911_WriteRegister(TSL25911_REG_NPAILTL, TSL25911_Sensor.ALS.FullArray, 4);
}

/**
 * @brief Sets the persistence filter for ALS interrupts.
 * 
 * @param persistenceValue Desired persistence value.
 * @return HAL_OK if successful, HAL_ERROR otherwise.
 */
HAL_StatusTypeDef TSL25911_SetPersistence(TSL25911_PERSIST_t persistenceValue) {
    TSL25911_Sensor.PERSIST = persistenceValue;
    return TSL25911_WriteRegister(TSL25911_REG_PERSIST, &TSL25911_Sensor.PERSIST, 1);
}

/**
 * @brief Reads the device ID of the TSL2591 sensor.
 * 
 * @return HAL_OK if successful, HAL_ERROR otherwise.
 */
HAL_StatusTypeDef TSL25911_ReadID(void) {
    return TSL25911_ReadRegister(TSL25911_REG_ID, &TSL25911_Sensor.ID, 1);
}

/**
 * @brief Reads the status register of the TSL2591 sensor.
 * 
 * @return HAL_OK if successful, HAL_ERROR otherwise.
 */
HAL_StatusTypeDef TSL25911_GetStatus(void) {
    return TSL25911_ReadRegister(TSL25911_REG_STATUS, &TSL25911_Sensor.STATUS.Val.Value, 1);
}

/**
 * @brief Clears an interrupt on the TSL2591 sensor.
 * 
 * @param interrupt Type of interrupt to clear (special function command).
 * @return HAL_OK if successful, HAL_ERROR otherwise.
 */
HAL_StatusTypeDef TSL25911_ClearInterrupt(TSL25911_SpecialFunction_t interrupt) {
    return HAL_I2C_Master_Transmit(&hi2c1, TSL25911_I2C_ADDR, (uint8_t*)&interrupt, 1, HAL_MAX_DELAY);
}

/**
 * @brief Reads light data from the TSL2591 sensor.
 * 
 * This function performs the following steps:
 * 1. Reads the status register to check the validity of the data using TSL25911_GetStatus.
 * 2. Reads the raw light data directly into the mapped data structure using ReadRegister.
 * 3. Maps the raw data to the light data structure.
 * 4. Calculates the lux value based on the raw data, gain, and integration time.
 * 5. Clears the ALS interrupt if it is set.
 * 
 * @param lightData Pointer to a structure to store the light data.
 * @return HAL_OK if successful, HAL_ERROR otherwise.
 */
HAL_StatusTypeDef TSL25911_ReadLightData(TSL25911_LightData_t *lightData) {
    /* Step 1: Read the status register to verify data validity */
    if (TSL25911_GetStatus() != HAL_OK) {
        return HAL_ERROR; // I2C communication failure
    }

    /* Check if the RGBC/ALS cycle has completed (AVALID bit) */
    if (!TSL25911_Sensor.STATUS.Val.BitField.AVALID) {
        /* CRITICAL: Clear the interrupt even if data is not valid. 
         * This ensures the sensor triggers a new cycle and the INT pin 
         * releases, preventing the sensor from reporting no more data. */
        TSL25911_ClearInterrupt(TSL25911_SPECIAL_FUNCTION_CLEAR_ALS_INT);
        return HAL_BUSY; 
    }

    /* Step 2: Read raw light data directly into the mapped data structure */
    if (TSL25911_ReadRegister(TSL25911_REG_C0DATA, TSL25911_Sensor.DATA.Array, sizeof(TSL25911_Sensor.DATA.Array)) != HAL_OK) {
        return HAL_ERROR; // I2C read operation failed
    }

    /* Step 3: Map raw data to the light data structure */
    lightData->FullSpectrum = TSL25911_Sensor.DATA.Channels.CH0.Value;
    lightData->Infrared = TSL25911_Sensor.DATA.Channels.CH1.Value;
    lightData->Visible = (lightData->FullSpectrum > lightData->Infrared) ? (lightData->FullSpectrum - lightData->Infrared) : 0;

    /* Step 4: Calculate lux based on integration time, gain, and raw data */
    float atime, again, cpl;
    
    // Determine Integration Time (ATIME)
    switch (TSL25911_Sensor.CTRL.Val.BitField.ATIME) {
        case TSL25911_INTEGRATION_100MS: atime = 100.0F; break;
        case TSL25911_INTEGRATION_200MS: atime = 200.0F; break;
        case TSL25911_INTEGRATION_300MS: atime = 300.0F; break;
        case TSL25911_INTEGRATION_400MS: atime = 400.0F; break;
        case TSL25911_INTEGRATION_500MS: atime = 500.0F; break;
        case TSL25911_INTEGRATION_600MS: atime = 600.0F; break;
        default: atime = 100.0F; break;
    }

    // Determine Gain (AGAIN)
    switch (TSL25911_Sensor.CTRL.Val.BitField.AGAIN) {
        case TSL25911_GAIN_LOW:  again = 1.0F; break;
        case TSL25911_GAIN_MED:  again = 24.5F; break;
        case TSL25911_GAIN_HIGH: again = 400.0F; break;
        case TSL25911_GAIN_MAX:  again = 9200.0F; break;
        default: again = 1.0F; break;
    }

    // Check for sensor saturation/overflow
    if (lightData->FullSpectrum == 0xFFFF || lightData->Infrared == 0xFFFF) {
        /* Clear interrupt before exiting on overflow */
        TSL25911_ClearInterrupt(TSL25911_SPECIAL_FUNCTION_CLEAR_ALS_INT);
        return HAL_ERROR; 
    }

    // Final Lux Calculation
    if (lightData->FullSpectrum == 0) {
        lightData->Lux = 0.0F;
    } else {
        cpl = (atime * again) / TSL25911_LUX_DF;
        lightData->Lux = (((float)lightData->Visible) * (1.0F - ((float)lightData->Infrared / (float)lightData->FullSpectrum))) / cpl;
    }

    /* Step 5: Clear the ALS interrupt after a successful read */
    if (TSL25911_ClearInterrupt(TSL25911_SPECIAL_FUNCTION_CLEAR_ALS_INT) != HAL_OK) {
        return HAL_ERROR;
    }

    return HAL_OK;
}
